AtlasFPGA/ESP32-ATLAS/FOTOS/Recolocador_ESP32_DEVKIT_V1_SUPERIOR.png

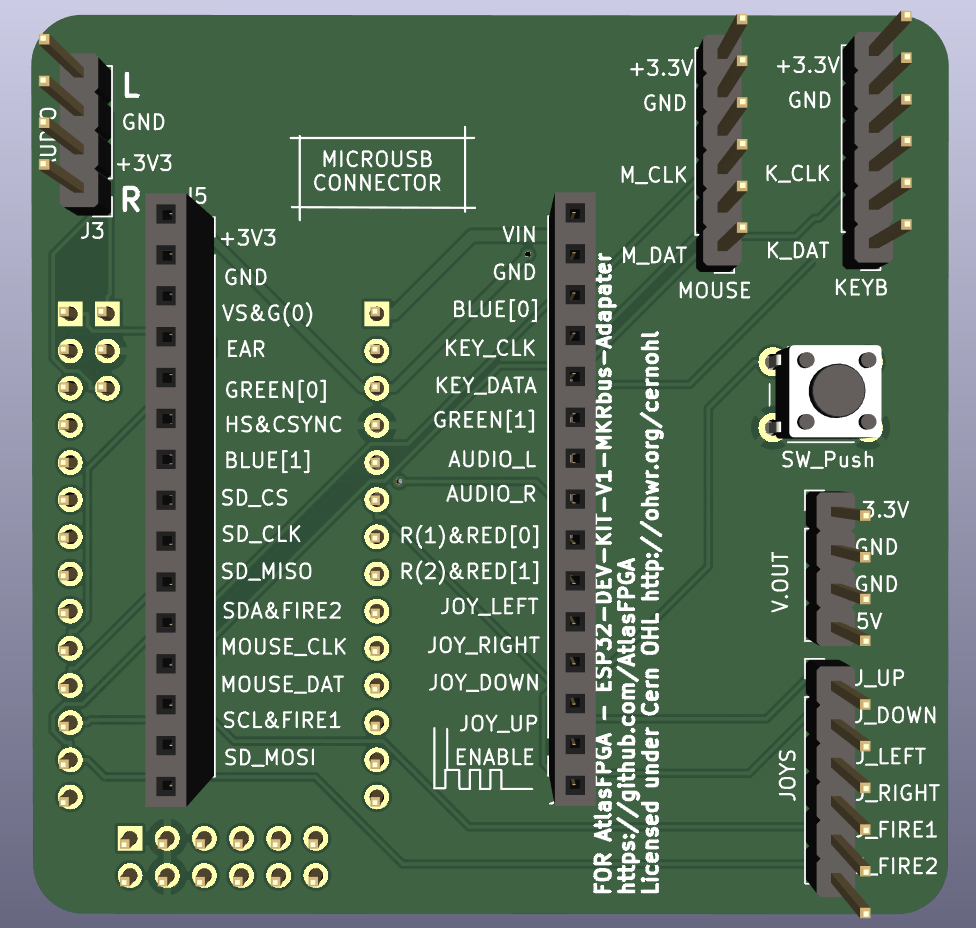
FOTOS/Recolocador_ESP32_DEVKIT_V1_SUPERIOR.png
