AtlasFPGA/ESP32-ATLAS/FOTOS_PLACA_REALES/P1050204.JPG

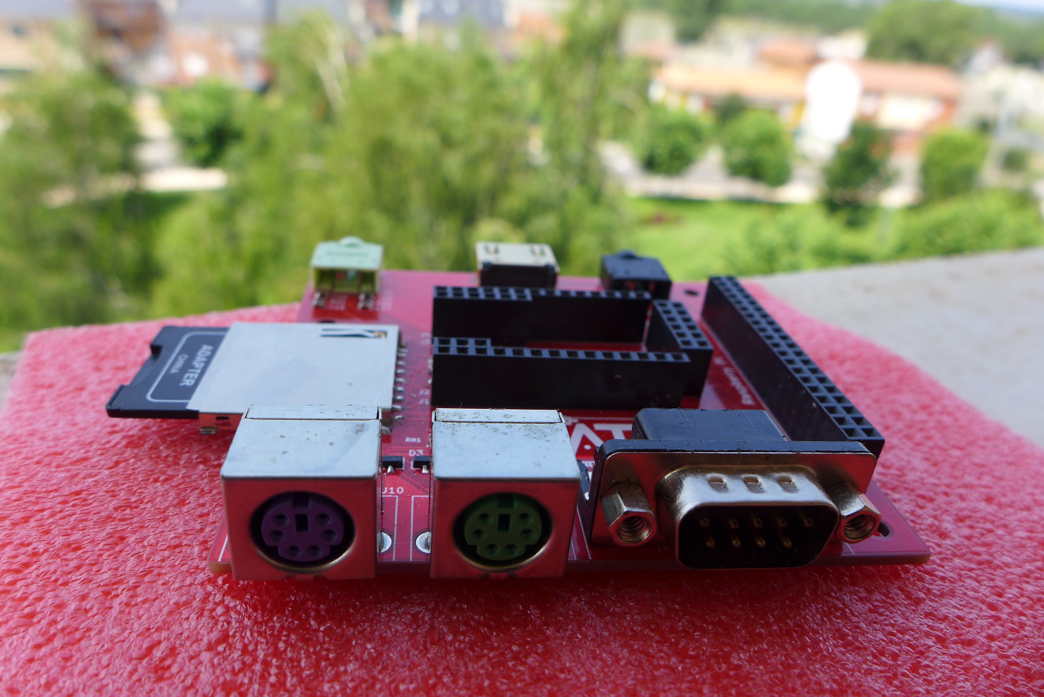
FOTOS_PLACA_REALES/P1050204.JPG
